Chrismettal/EleLab_v2/img/24vInterface.jpg

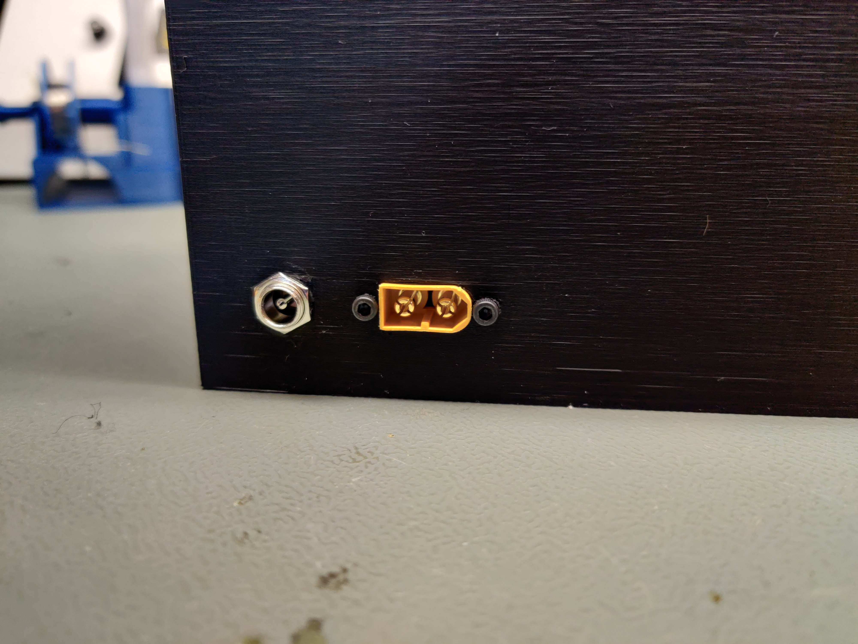
img/24vInterface.jpg
