Chrismettal/EleLab_v2/img/24vOpen.jpg

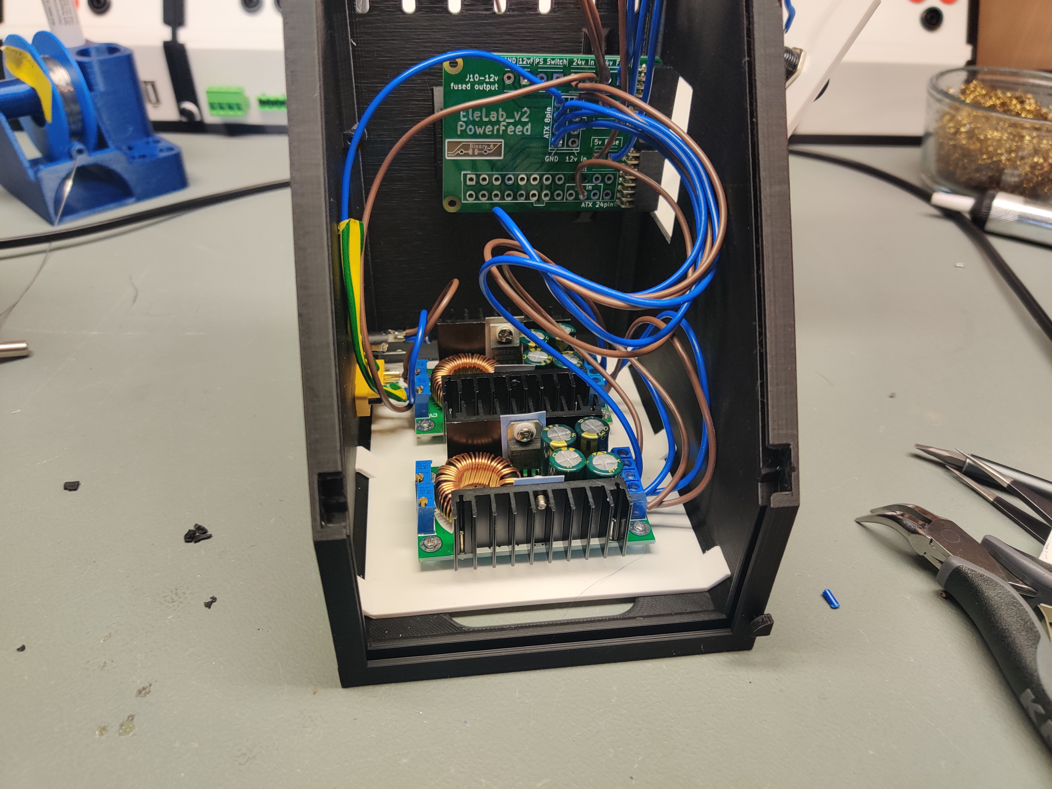
img/24vOpen.jpg
