Chrismettal/EleLab_v2/img/ATX.jpg

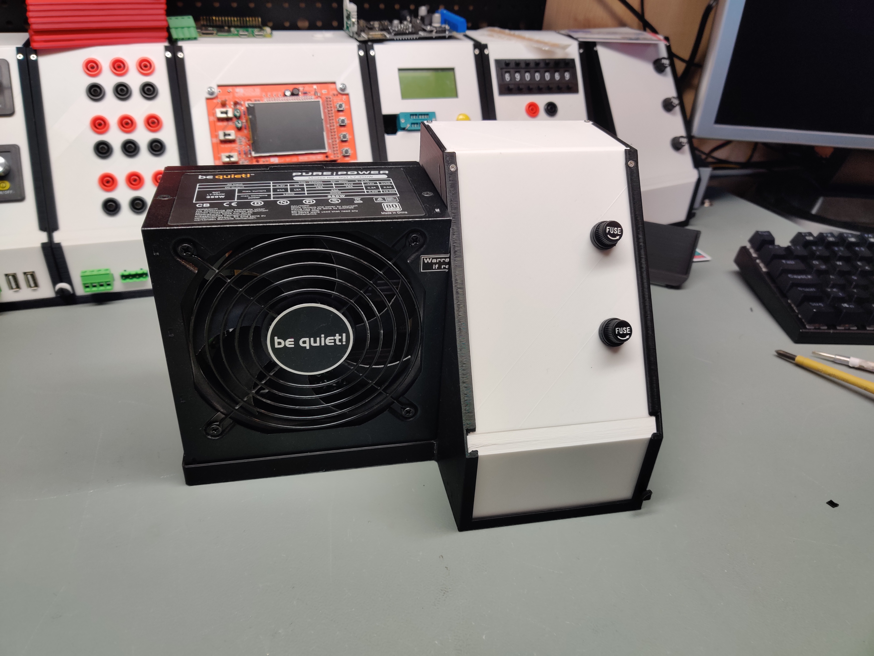
img/ATX.jpg
