Chrismettal/EleLab_v2/img/Banana.jpg

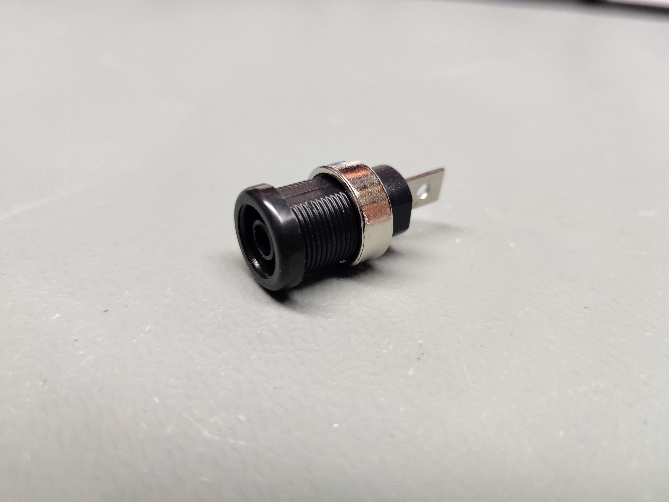
img/Banana.jpg
