Chrismettal/EleLab_v2/img/Complete.jpg

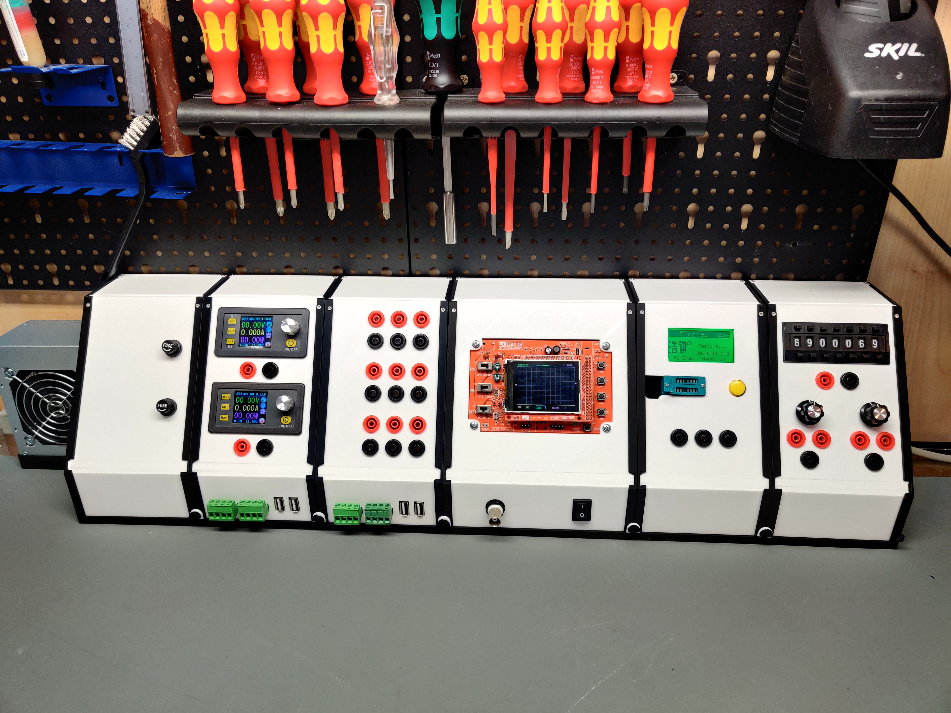
img/Complete.jpg
