Chrismettal/EleLab_v2/img/Display_AngledCables.jpg

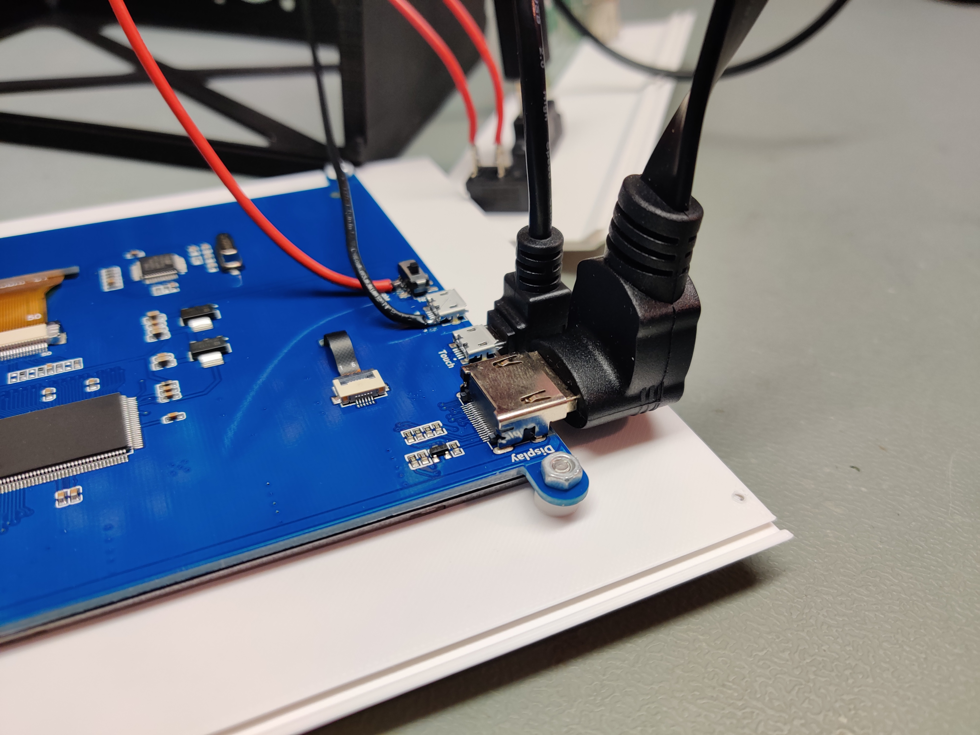
img/Display_AngledCables.jpg
