Chrismettal/EleLab_v2/img/EmptyFrame.jpg

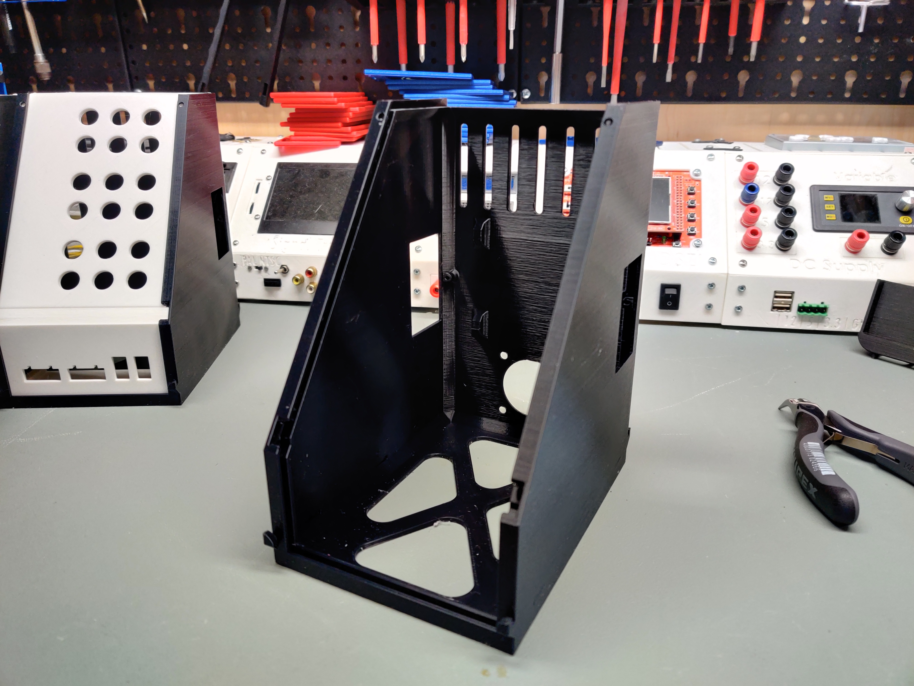
img/EmptyFrame.jpg
