Chrismettal/EleLab_v2/img/Frontpanel_a_2.jpg

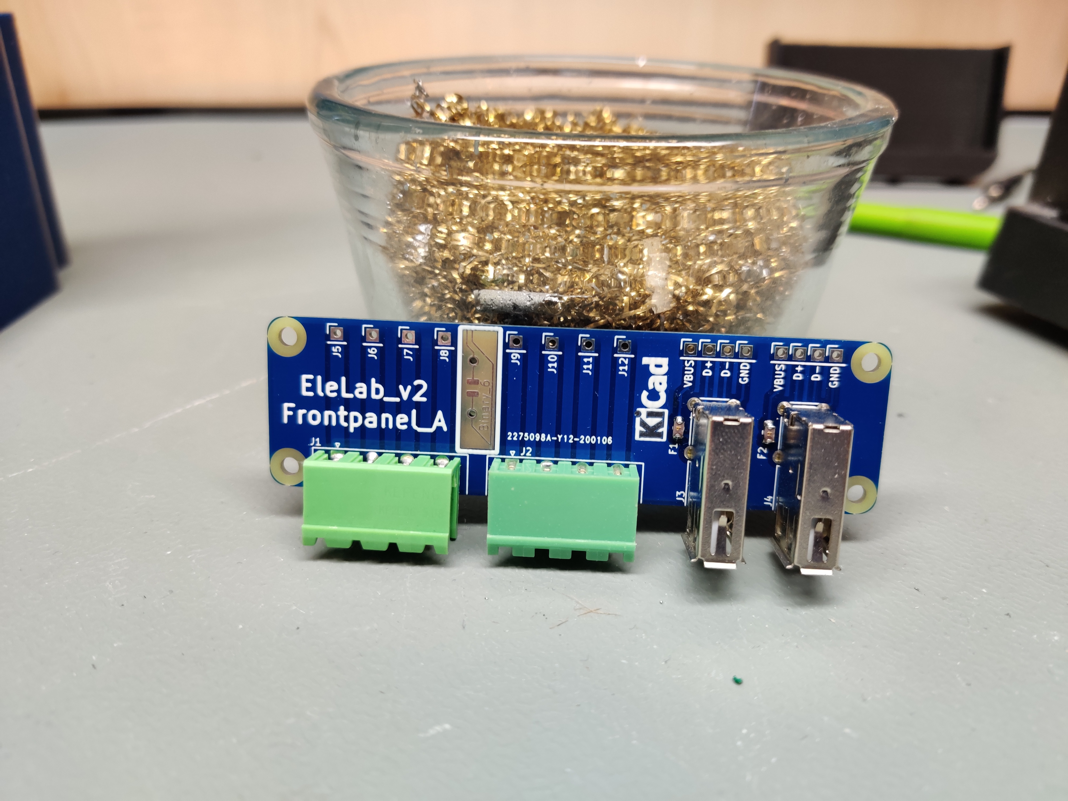
img/Frontpanel_a_2.jpg
