Chrismettal/EleLab_v2/img/Interface_.jpg

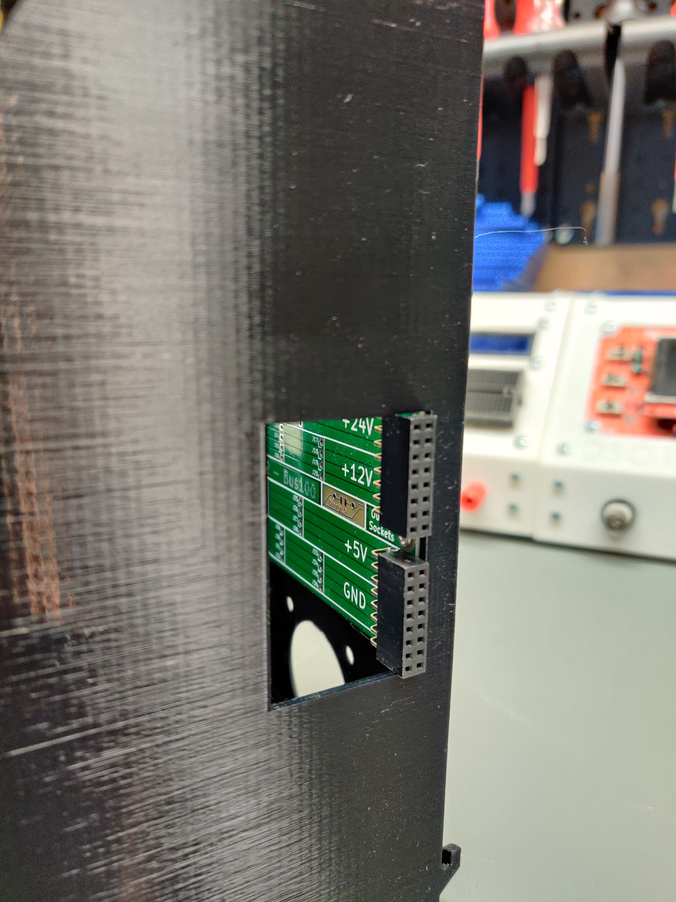
img/Interface_.jpg
