Chrismettal/EleLab_v2/img/Interface_Male.jpg

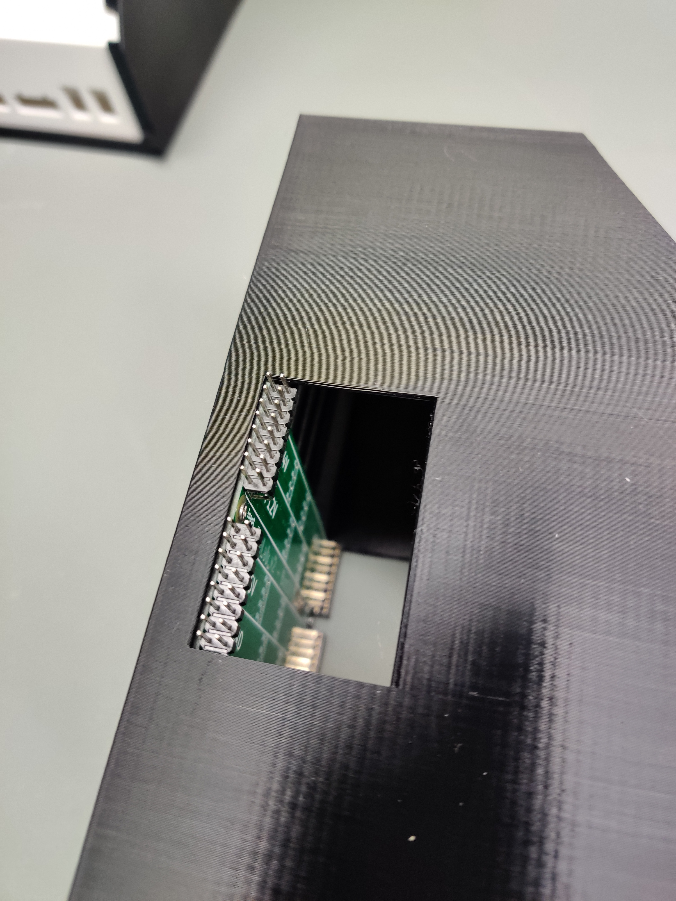
img/Interface_Male.jpg
