Chrismettal/EleLab_v2/img/LabVar_6.jpg

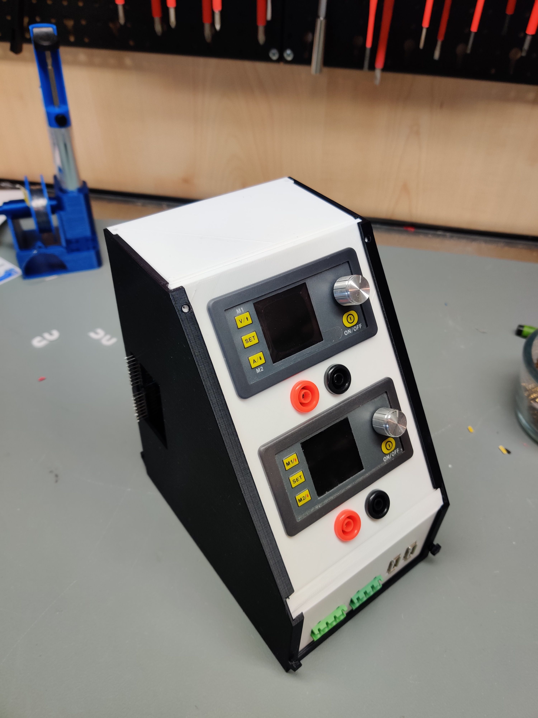
img/LabVar_6.jpg
