Chrismettal/EleLab_v2/img/SecondDocked2.jpg

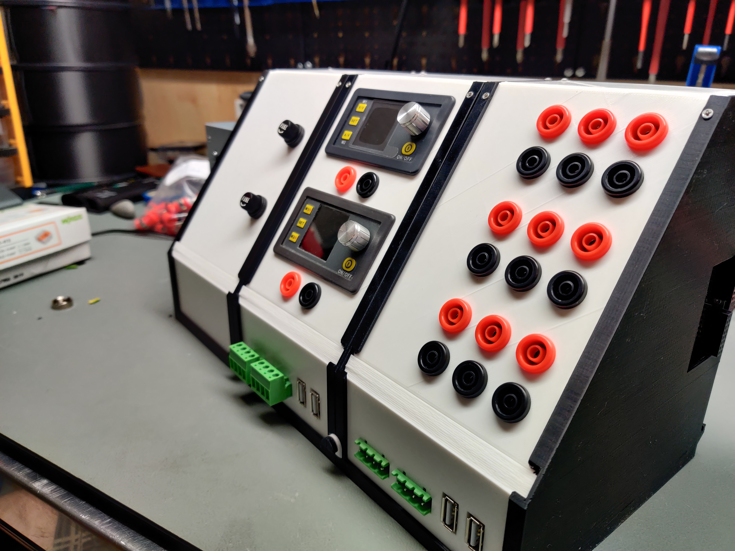
img/SecondDocked2.jpg
