Chrismettal/EleLab_v2/img/SecondDocked.jpg

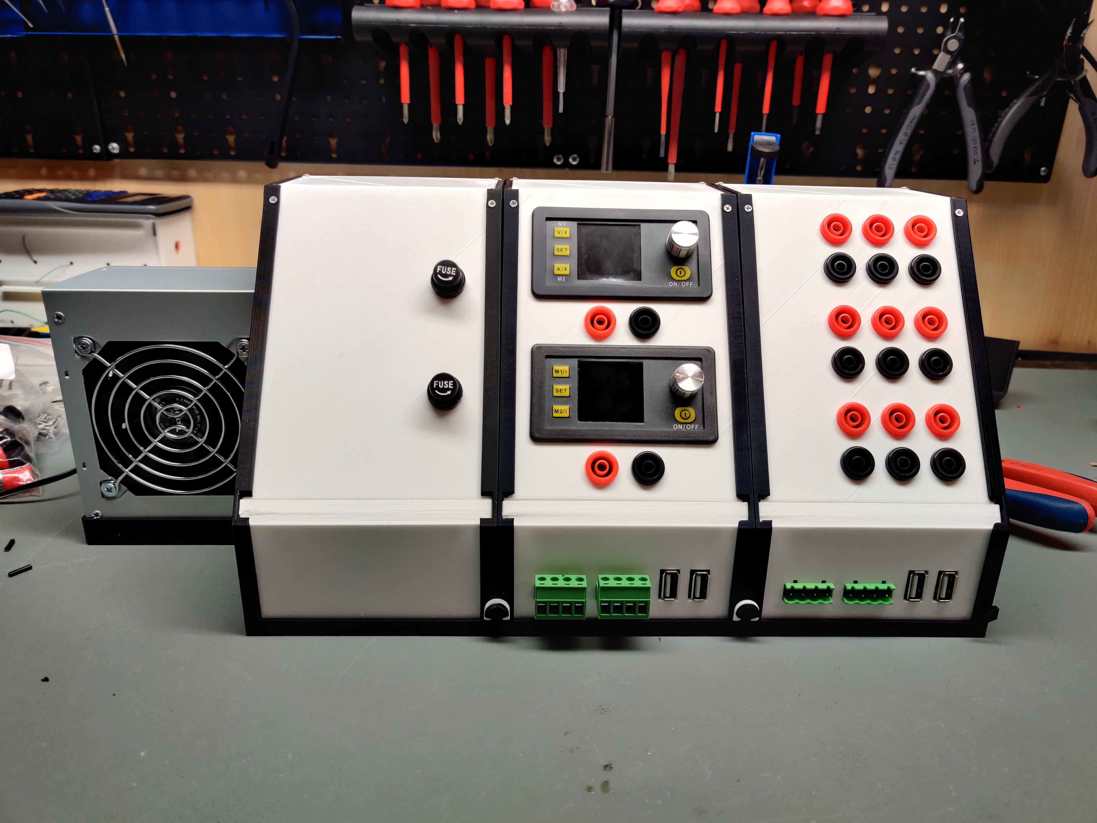
img/SecondDocked.jpg
