Chrismettal/EleLab_v2/img/Interfacing.jpg

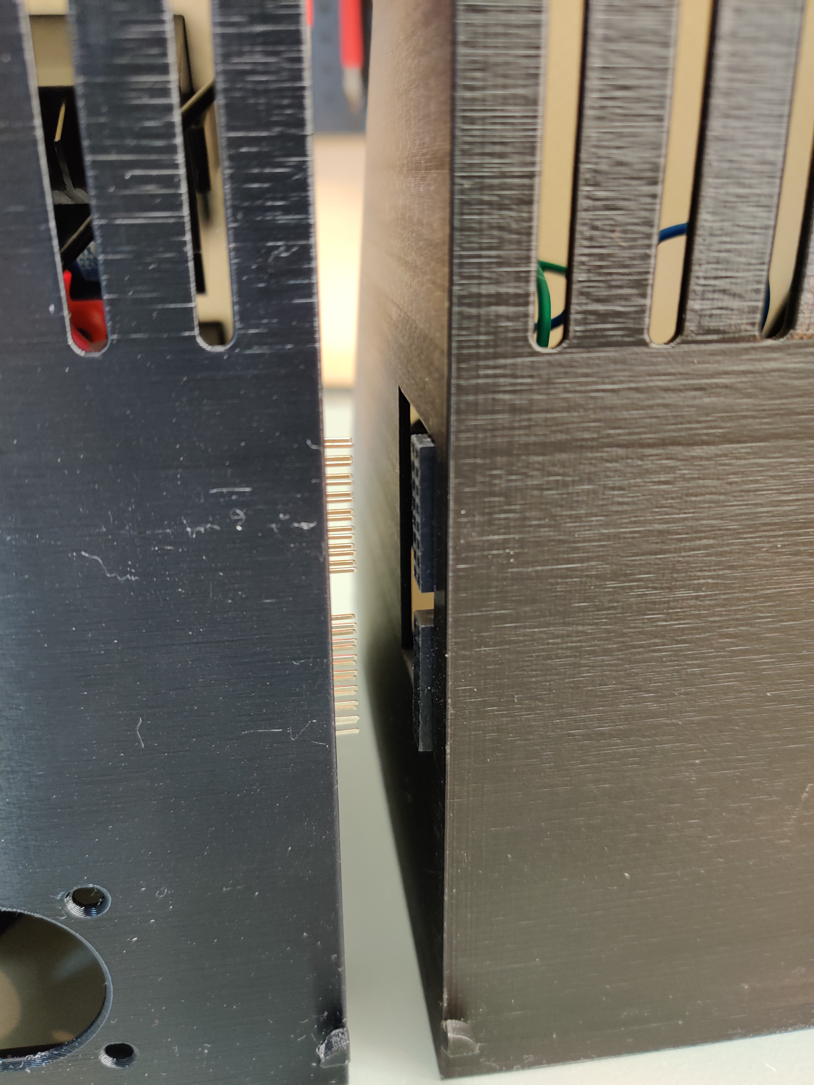
img/Interfacing.jpg
